anthal/Display-VQB71-TM1637/Pictures/20230818_075816.jpg

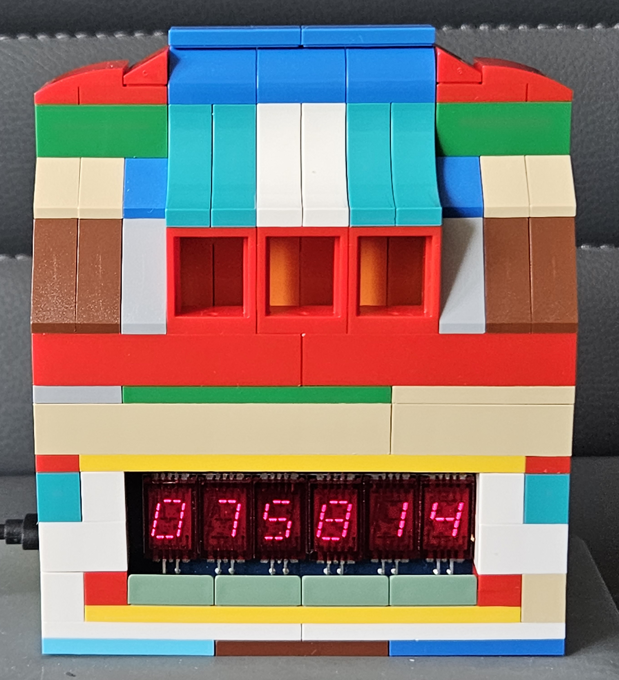
Pictures/20230818_075816.jpg
