anthal/Display-VQB71-TM1637/Pictures/20230820_180819.jpg

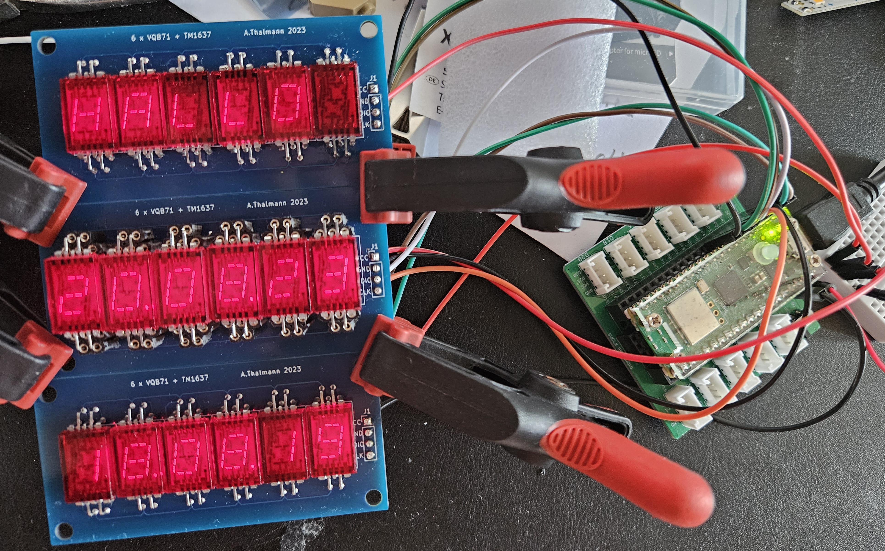
Pictures/20230820_180819.jpg
