anthal/Display-VQB71-TM1637/MicroPython/WizFi360-EVB-Pico/secrets.py

secrets = {
    'ssid': 'anth-0',
    'key': 'anthal-17!'
    }

# US:
# 'ntp-server': '"cn.ntp.org.cn","ntp.sjtu.edu.cn","us.pool.ntp.org"'
# DE:
#'ntp-server': '"ntp1.t-online.de","de.pool.ntp.org","ptbtime1.ptb.de"',  
# Local:
#'ntp-server': '"192.168.0.1"'

network = {
    'ntp-server': '"ntp1.t-online.de","de.pool.ntp.org","ptbtime1.ptb.de"',
    }
