anthal/Display-VQB71-TM1637/MicroPython/settings.py

net = {
    'ssid': 'your ssid',
    'key': 'your key',
    'country': 'DE',
    }

mqtt = {
    'mqttBroker' = '192.168.0.111',
    'mqttClient' = 'RasPiPico',
    'mqttUser' = 'mqttUser',
    'mqttPW' = 'mqttPW',
    'mqttTopic' = b"mqttTopic"
    }

time = {
    'ntp_server': 'pool.ntp.org',
    # Sommerzeit:
    'gmt_offset': '2'
    # Winterzeit:
    #'gmt_offset': '1'
    }
